Haydeneagle/ultrasonic-tank-monitor/images/Demo/Dashboard.png

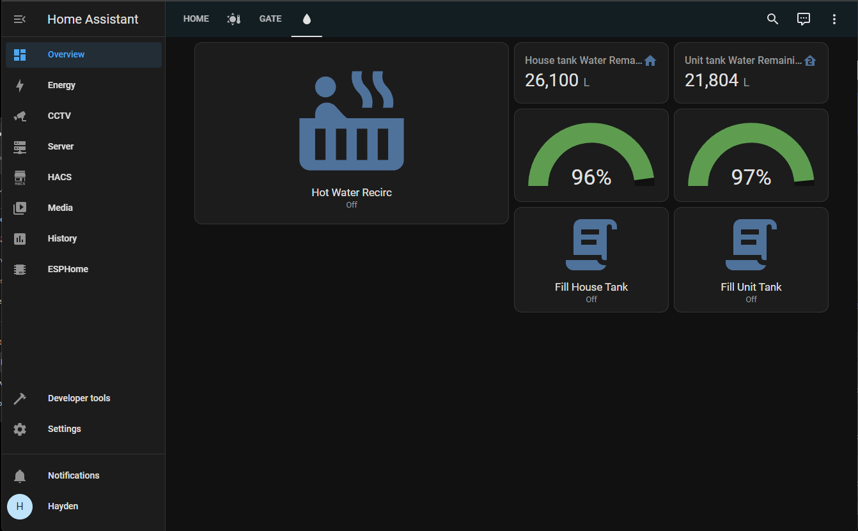
images/Demo/Dashboard.png
