Haydeneagle/ultrasonic-tank-monitor/images/Demo/Planned config page.png

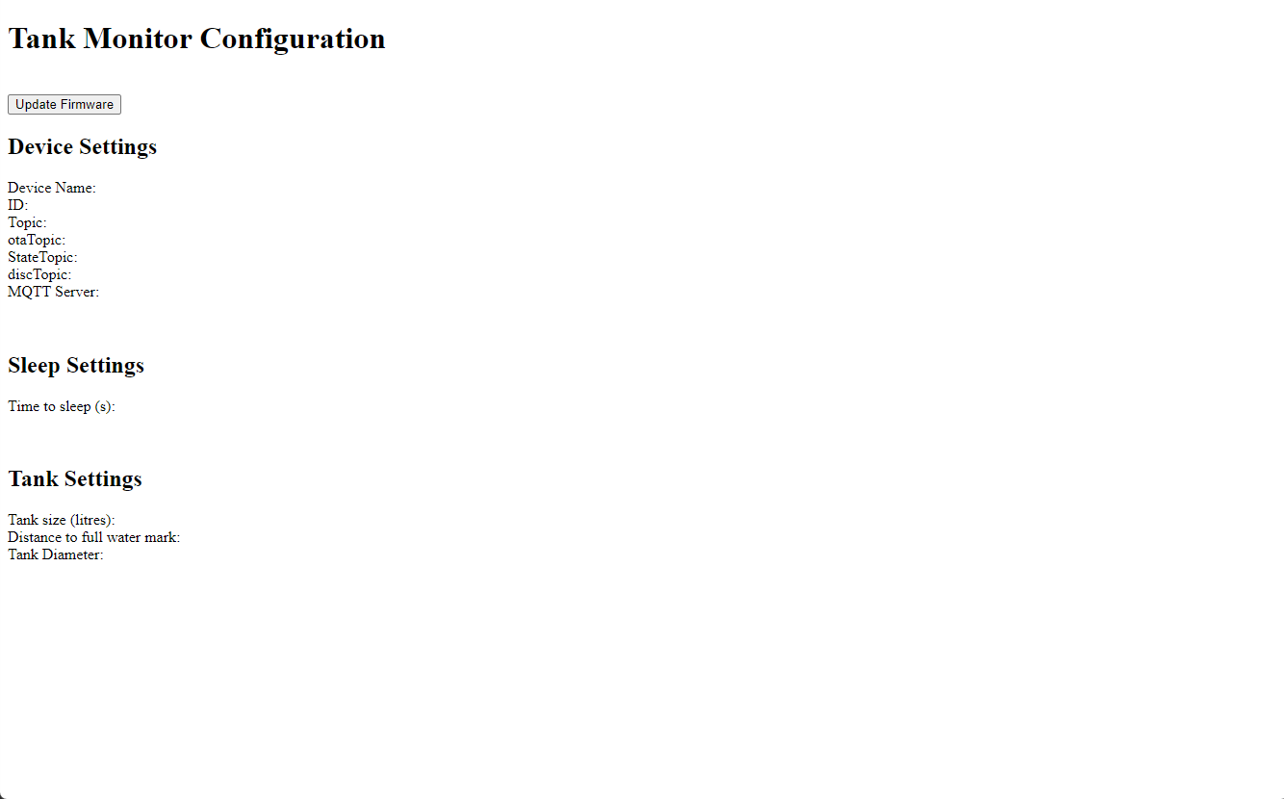
images/Demo/Planned config page.png
